NSE-labs/CoffeeRoasterV2/Documentation/Images/IMG_1774.JPG

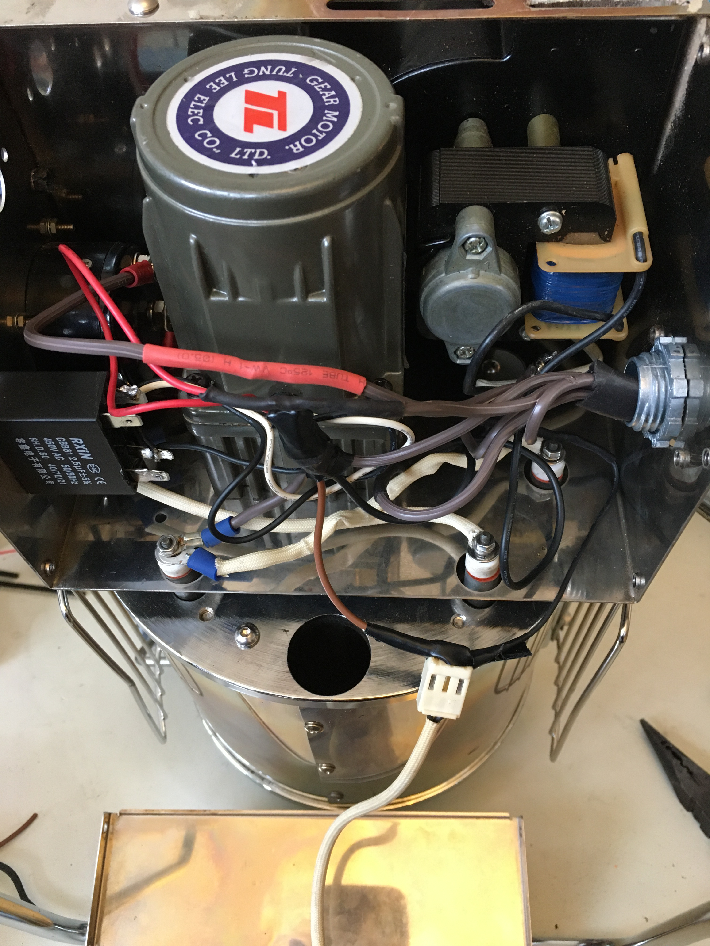
Documentation/Images/IMG_1774.JPG
