NSE-labs/CoffeeRoasterV2/Documentation/Images/IMG_1775.JPG

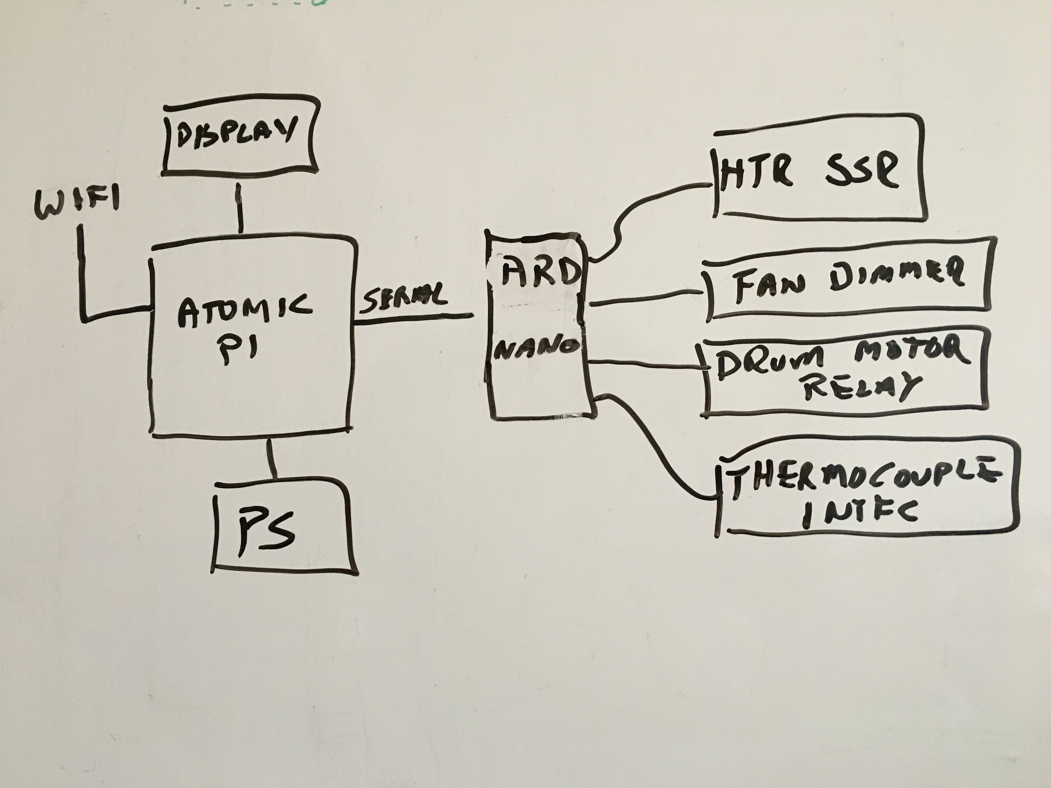
Documentation/Images/IMG_1775.JPG
