NSE-labs/CoffeeRoasterV2/Documentation/Images/IMG_1807.JPG

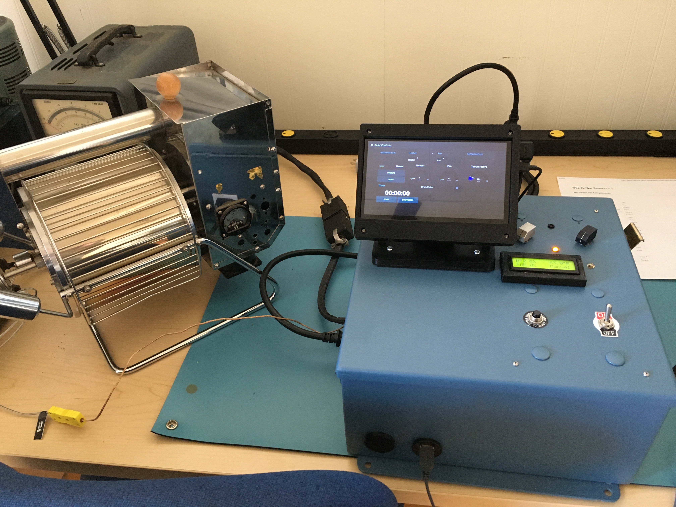
Documentation/Images/IMG_1807.JPG
