NSE-labs/CoffeeRoasterV2/Documentation/Images/IMG_1788.JPG

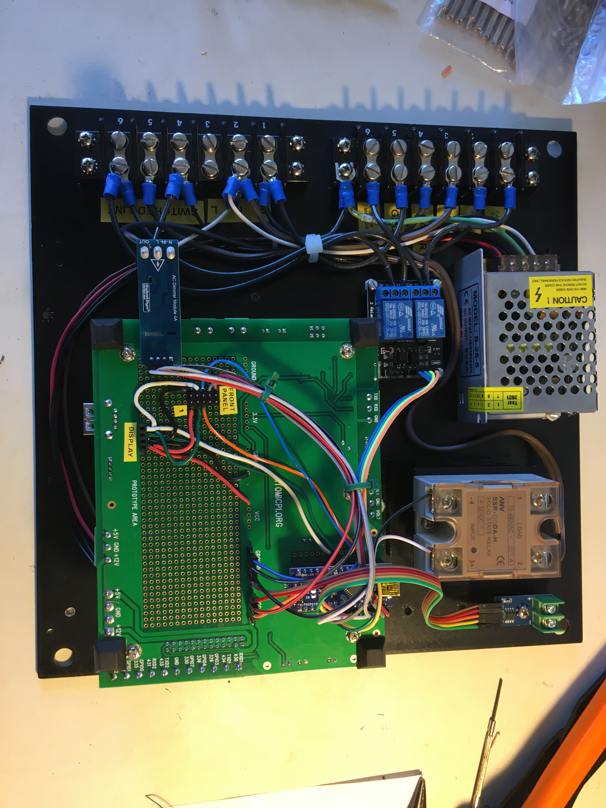
Documentation/Images/IMG_1788.JPG
