NSE-labs/CoffeeRoasterV2/Documentation/Images/IMG_1806.JPG

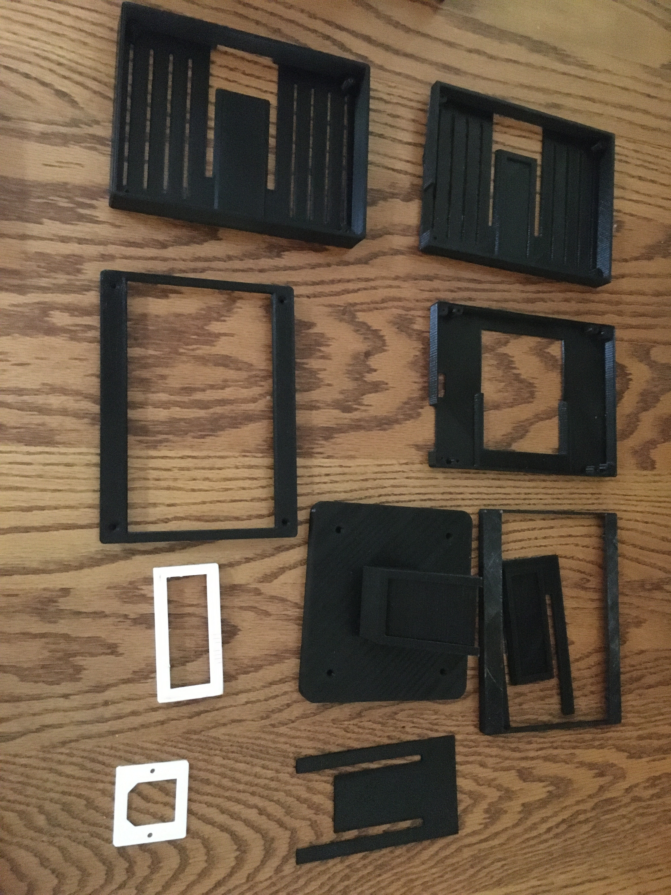
Documentation/Images/IMG_1806.JPG
